jcstarna/Hornos/docs/fotos/IMG-20210226-WA0007.jpg

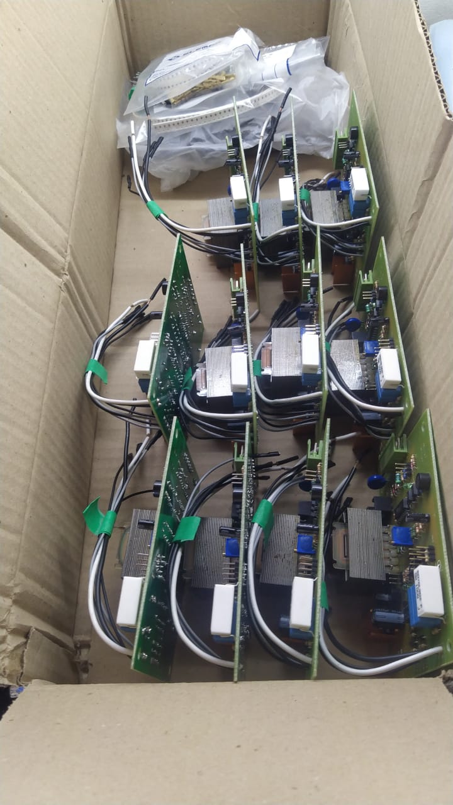
docs/fotos/IMG-20210226-WA0007.jpg
