jcstarna/Hornos/docs/fotos/IMG-20210729-WA0020.jpg

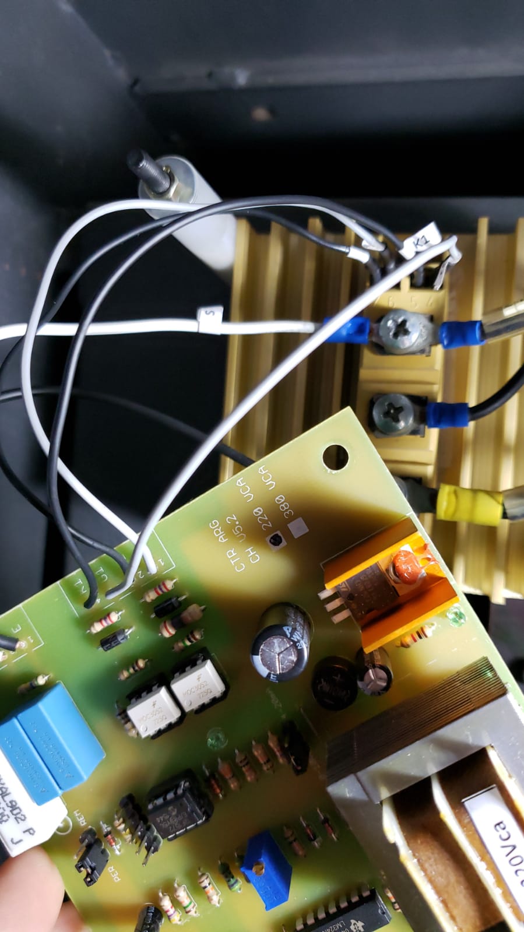
docs/fotos/IMG-20210729-WA0020.jpg
