jcstarna/Hornos/docs/fotos/WhatsApp Image 2022-01-06 at 09.14.48.jpeg

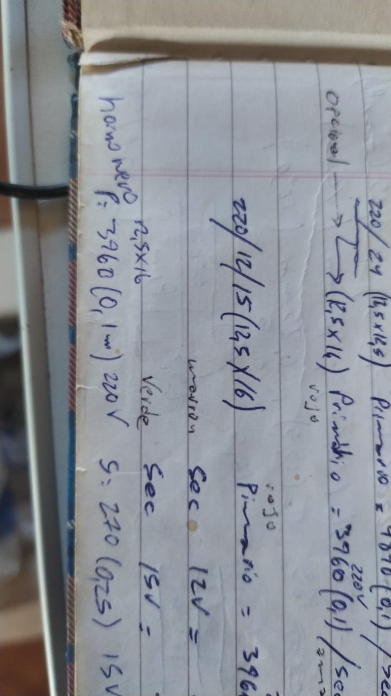
docs/fotos/WhatsApp Image 2022-01-06 at 09.14.48.jpeg
