jcstarna/Hornos/docs/fotos/WhatsApp Image 2022-01-06 at 09.16.51.jpeg

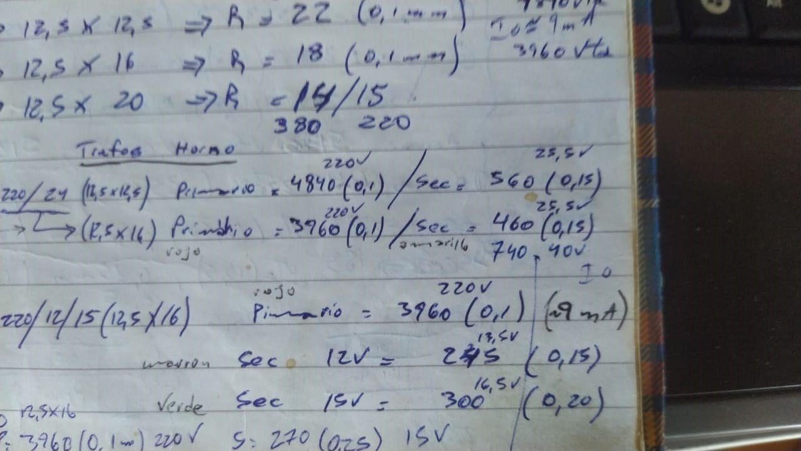
docs/fotos/WhatsApp Image 2022-01-06 at 09.16.51.jpeg
